ashishkumarpardeshi/ServerRoom-Monitoring-and-Alert-Device/Enclosure_Design/Enclosure_V1_3D_Images/Enc_3D_4.png

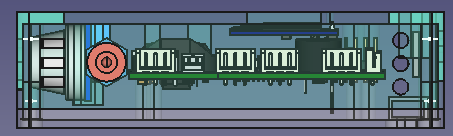
Enclosure_Design/Enclosure_V1_3D_Images/Enc_3D_4.png
