ashishkumarpardeshi/ServerRoom-Monitoring-and-Alert-Device/Enclosure_Design/Enclosure_V1_3D_Images/Enc_3D_8.png

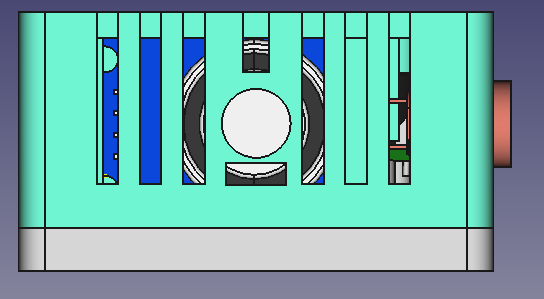
Enclosure_Design/Enclosure_V1_3D_Images/Enc_3D_8.png
