ashishkumarpardeshi/ServerRoom-Monitoring-and-Alert-Device/Enclosure_Design/Enclosure_V1_FreeCAD_Files/noun_Smoke_3394237.png

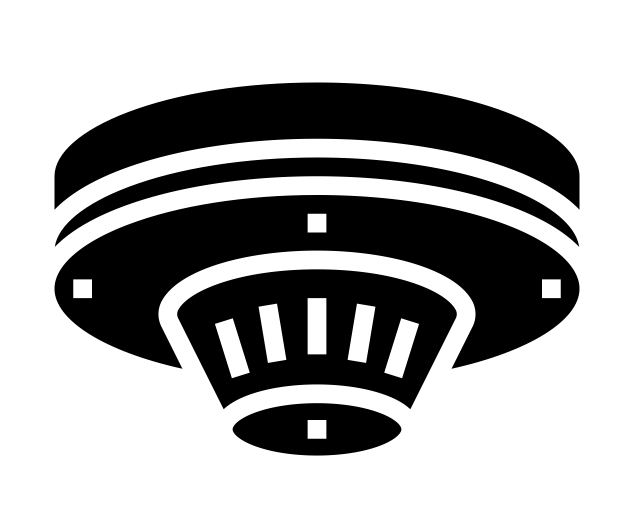
Enclosure_Design/Enclosure_V1_FreeCAD_Files/noun_Smoke_3394237.png
