ashishkumarpardeshi/ServerRoom-Monitoring-and-Alert-Device/PCB Design/PCB_Images/PWS1.jpg

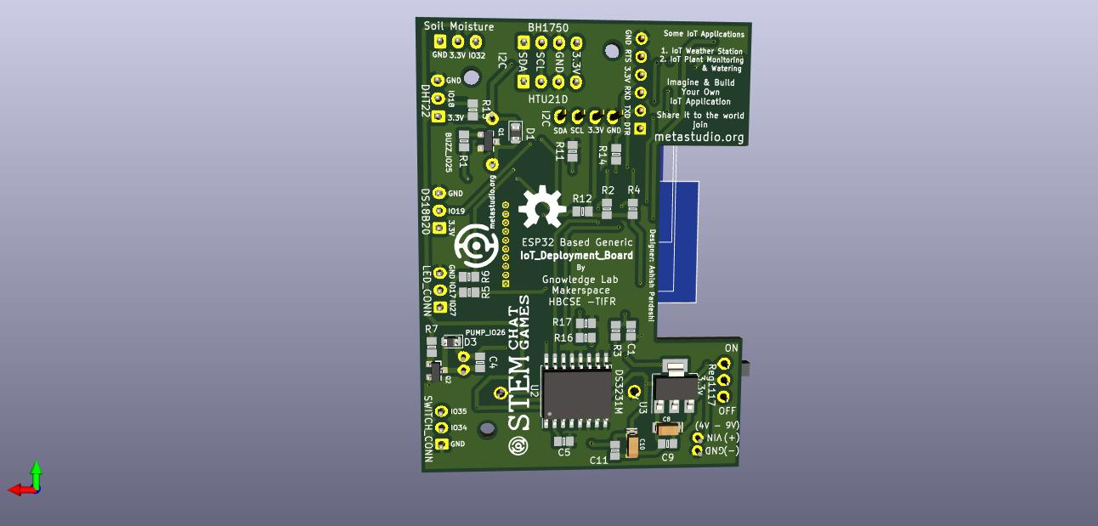
PCB Design/PCB_Images/PWS1.jpg
