ashishkumarpardeshi/ServerRoom-Monitoring-and-Alert-Device/PCB Design/PCB_Images/PWS5.jpg

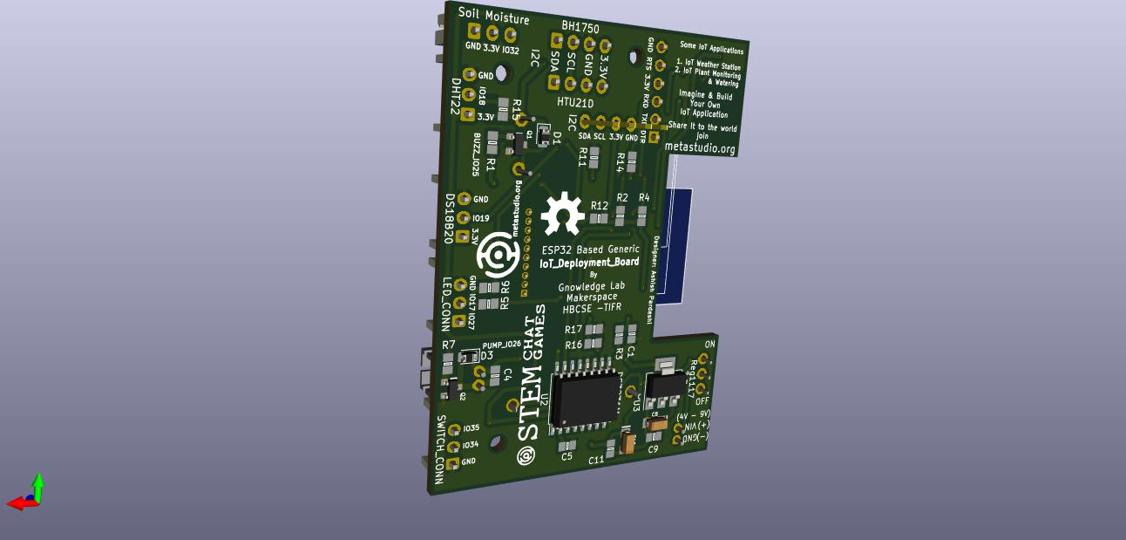
PCB Design/PCB_Images/PWS5.jpg
