ashishkumarpardeshi/ServerRoom-Monitoring-and-Alert-Device/PCB Design/PCB_Images/PWS6.jpg

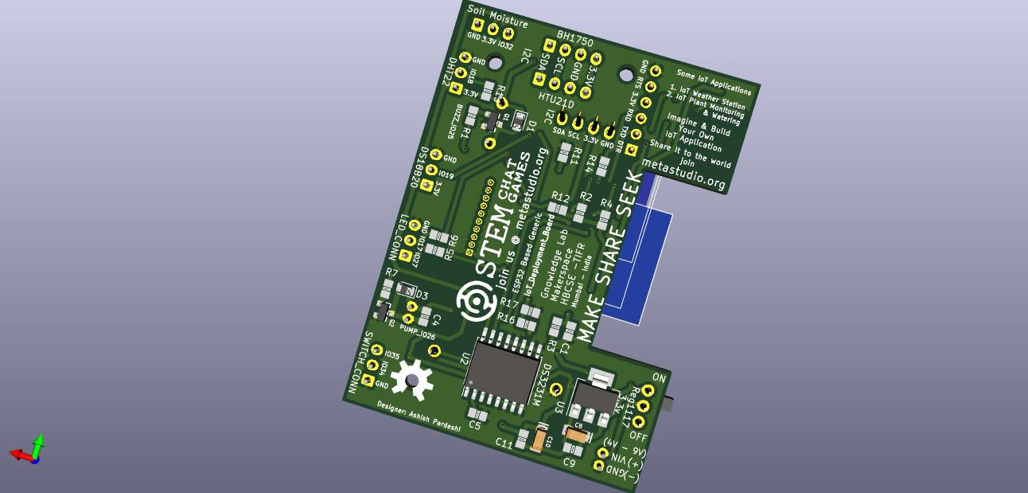
PCB Design/PCB_Images/PWS6.jpg
