ashishkumarpardeshi/ServerRoom-Monitoring-and-Alert-Device/PCB Design/PCB_Images/PWS8.jpg

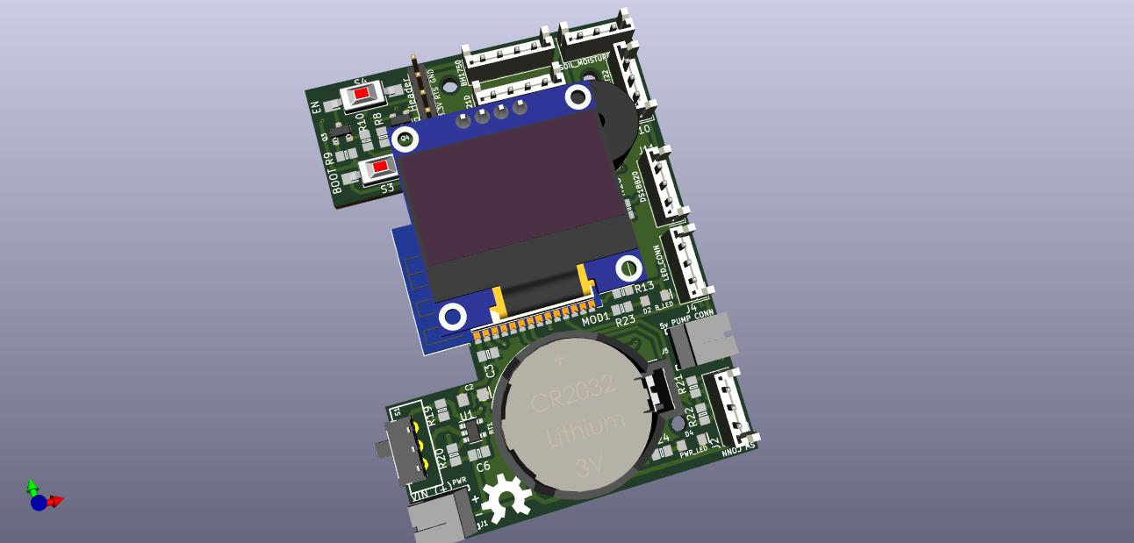
PCB Design/PCB_Images/PWS8.jpg
