ashishkumarpardeshi/ServerRoom-Monitoring-and-Alert-Device/PCB Design/PCB_Images/PWS10.jpg

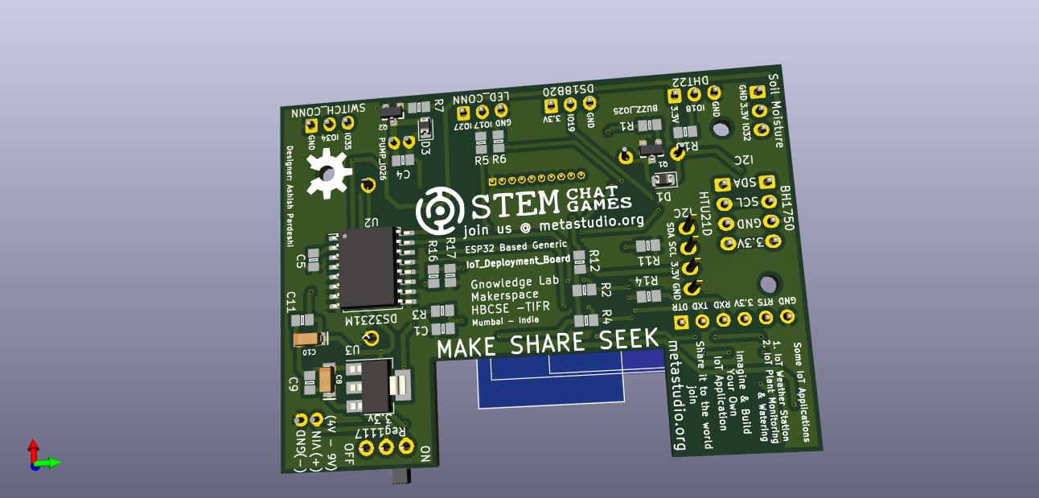
PCB Design/PCB_Images/PWS10.jpg
