ashishkumarpardeshi/ServerRoom-Monitoring-and-Alert-Device/PCB Design/SRMAD_PCB_KiCAD_Files/photo_2020-12-24_12-26-54.jpg

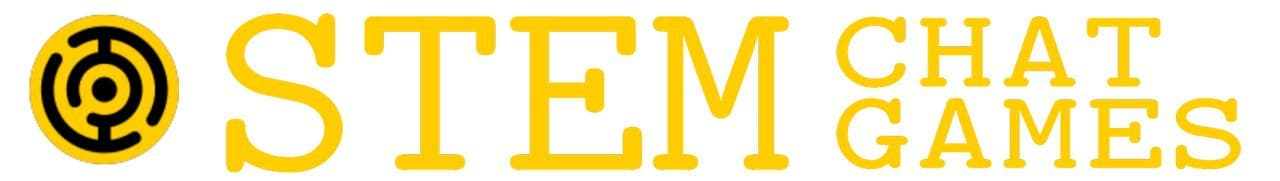
PCB Design/SRMAD_PCB_KiCAD_Files/photo_2020-12-24_12-26-54.jpg
